tongtongwang86/Revolute/Misc/Pictures V3/configurator/consumer.webp

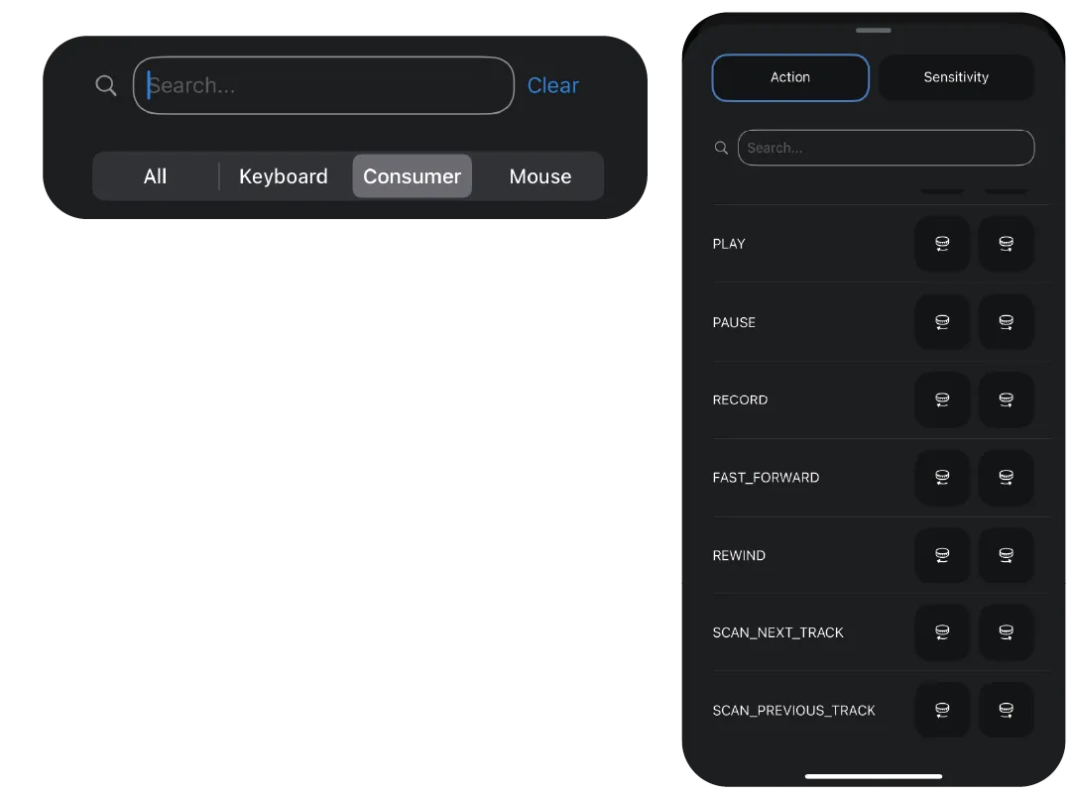
Misc/Pictures V3/configurator/consumer.webp
