tongtongwang86/Revolute/Misc/Pictures V3/configurator/dial.png

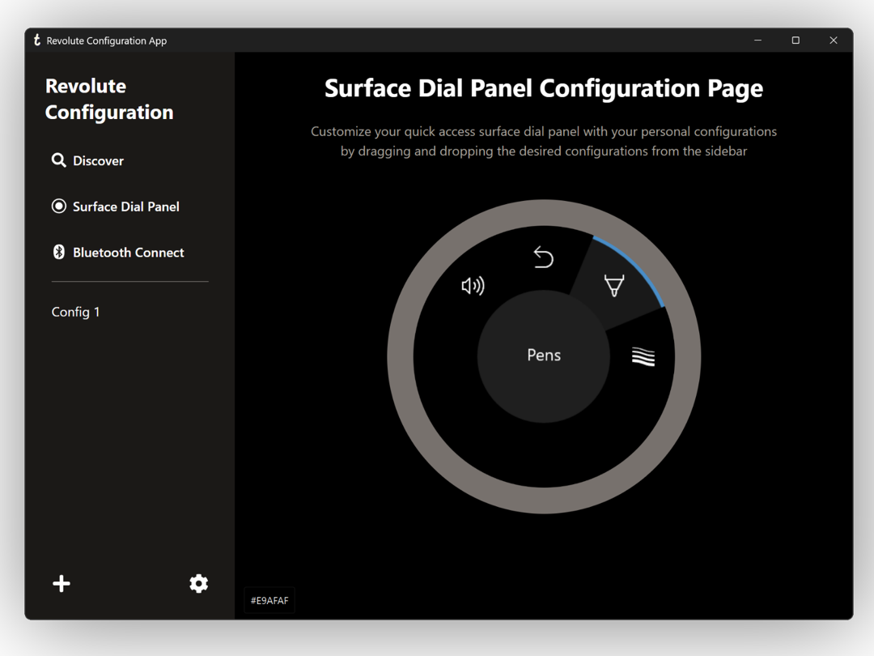
Misc/Pictures V3/configurator/dial.png
