tongtongwang86/Revolute/Misc/Pictures V3/configurator/mouse.webp

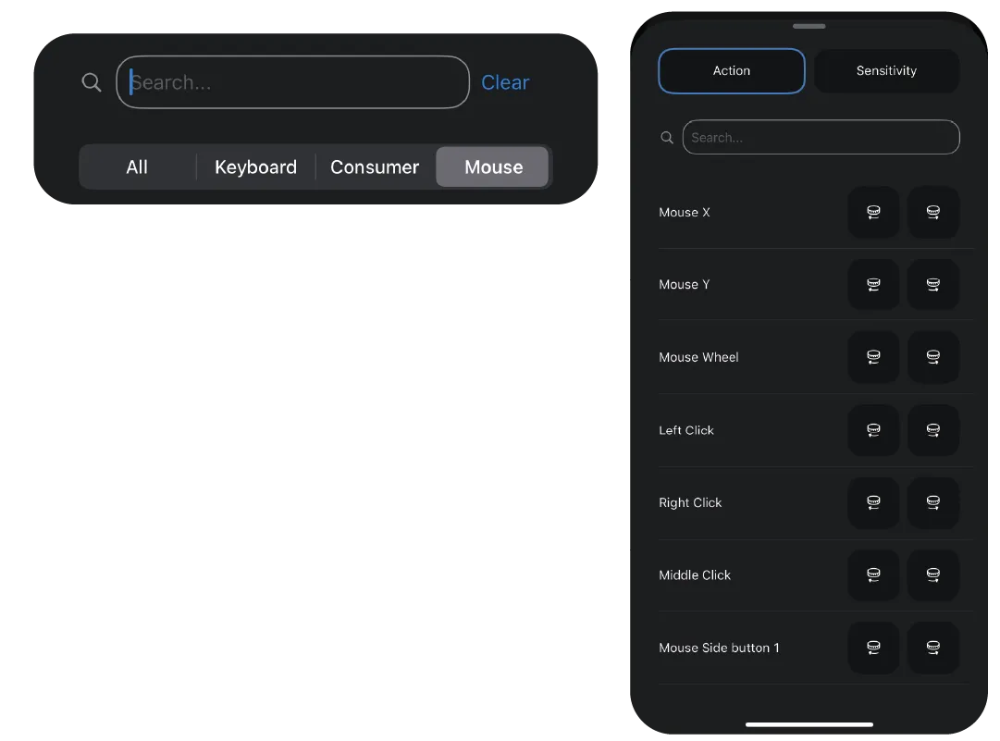
Misc/Pictures V3/configurator/mouse.webp
