tongtongwang86/Revolute/Misc/Pictures V3/configurator/scroll.webp

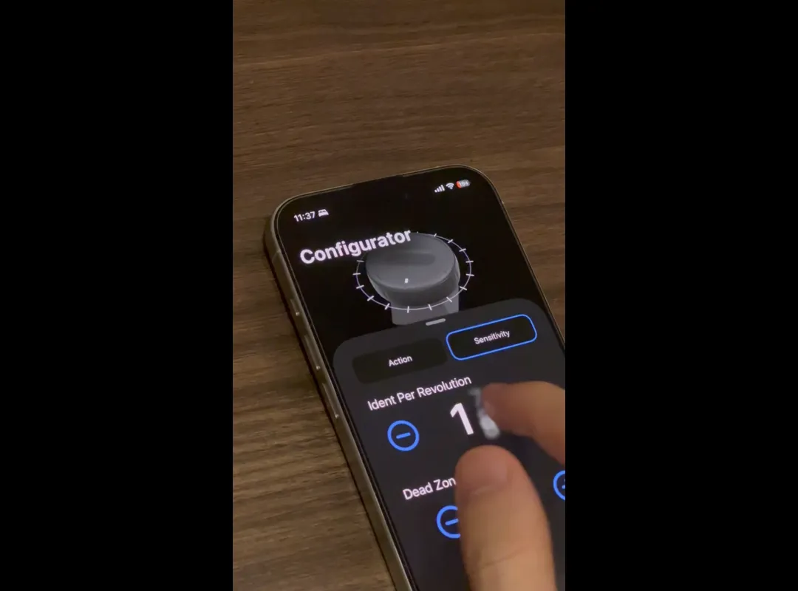
Misc/Pictures V3/configurator/scroll.webp
