tongtongwang86/Revolute/Misc/Pictures V3/demo/1.png

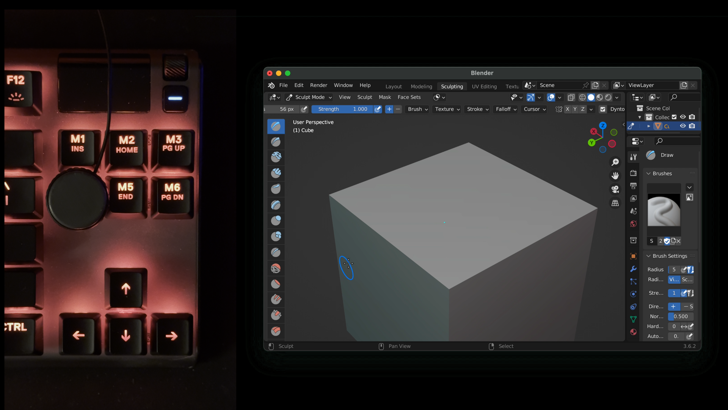
Misc/Pictures V3/demo/1.png
