tongtongwang86/Revolute/Misc/Pictures V3/demo/2.png

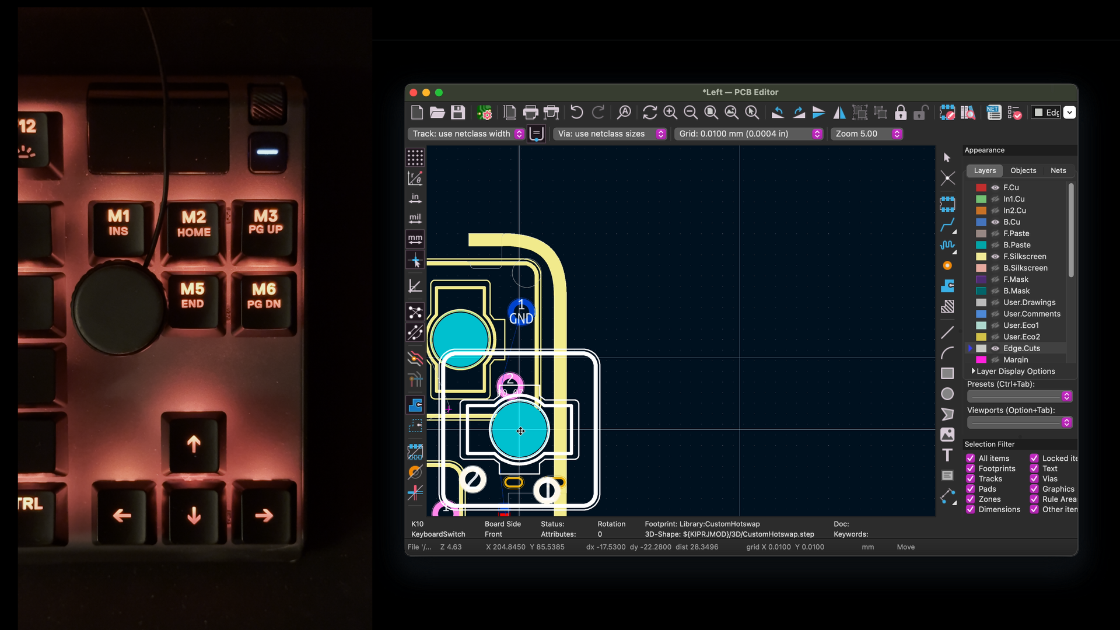
Misc/Pictures V3/demo/2.png
