tongtongwang86/Revolute/Misc/Pictures V3/demo/3.png

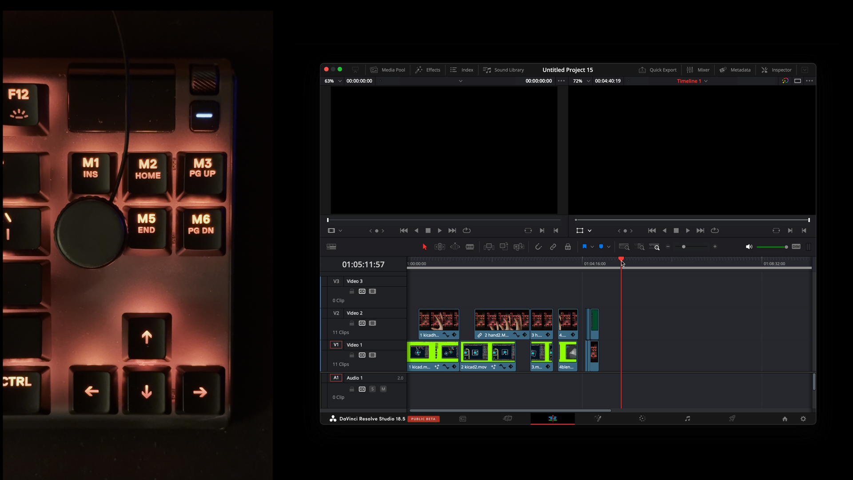
Misc/Pictures V3/demo/3.png
