tongtongwang86/Revolute/Misc/Pictures V3/demo/3_Small.png

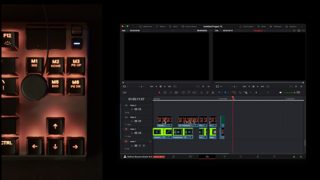
Misc/Pictures V3/demo/3_Small.png
