tongtongwang86/Revolute/Misc/Pictures V3/demo/4.png

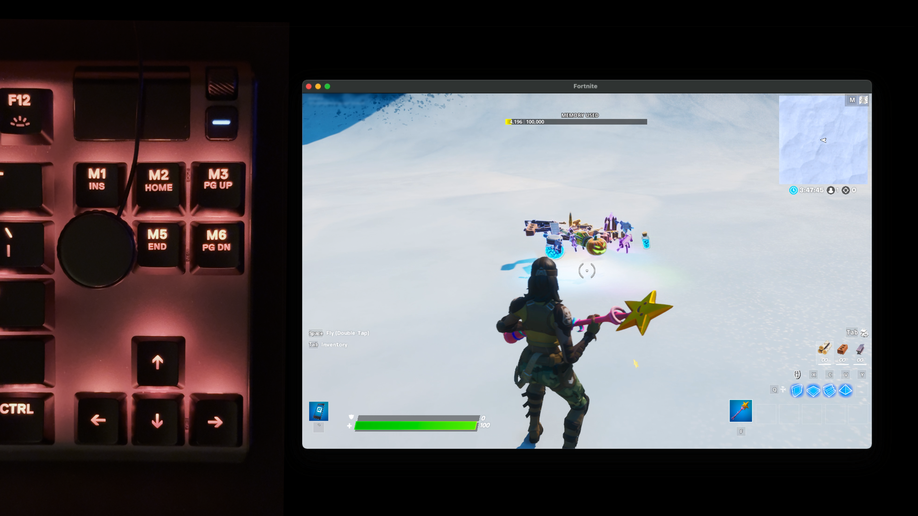
Misc/Pictures V3/demo/4.png
