tongtongwang86/Revolute/Misc/Pictures V3/poster/magtick.png

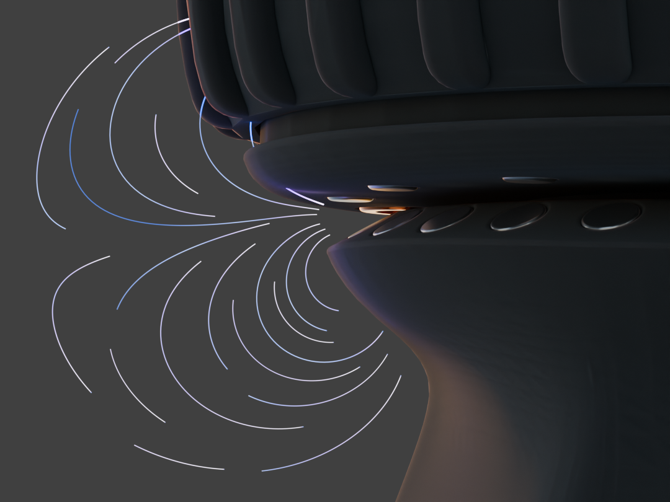
Misc/Pictures V3/poster/magtick.png
