tongtongwang86/Revolute/Hardware/Wired/TopPCB/TopPCB.step

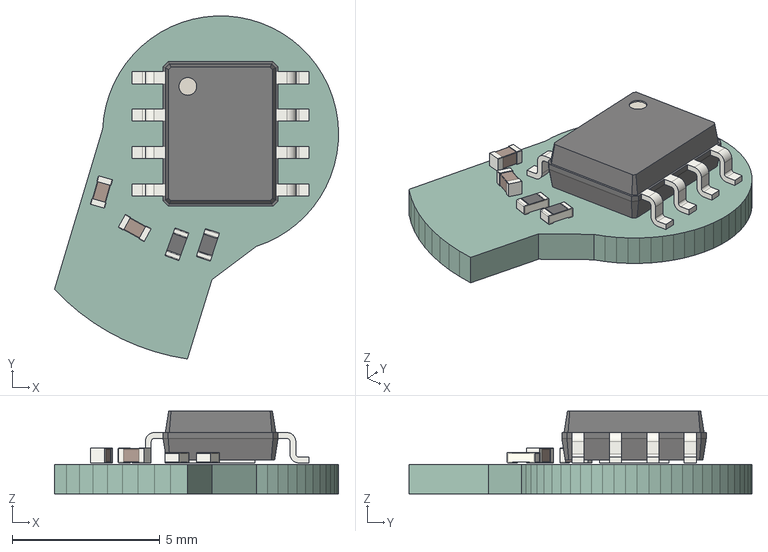
[picture p36: CAD file, 2023-05-05]
Hardware/Wired/TopPCB/TopPCB.step
9.63 x 11.6 x 2.80 mm
PCB
