tongtongwang86/Revolute/Hardware/Wired/TopPCB/wire.stl

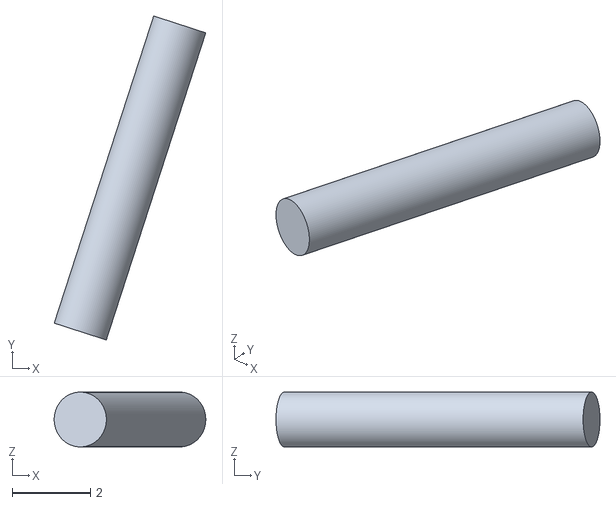
[picture p37: CAD file, 2023-05-05]
Hardware/Wired/TopPCB/wire.stl
3.87 x 8.27 x 1.40
