tongtongwang86/Revolute/Hardware/Debugger/3D/button v4.step

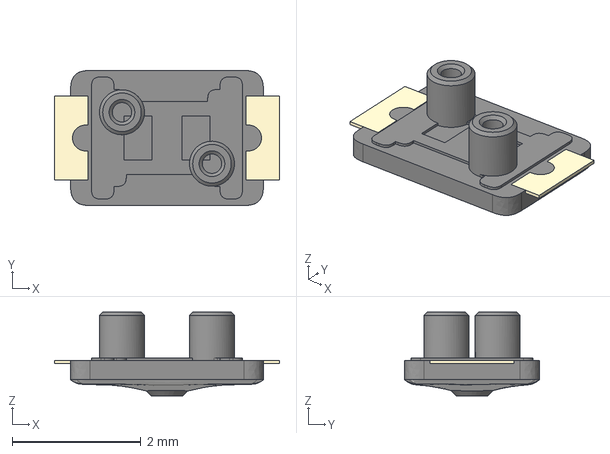
[picture p38: CAD file, 2024-02-21]
Hardware/Debugger/3D/button v4.step
3.50 x 2.10 x 1.30 mm
base
slider
