tongtongwang86/Revolute/Hardware/Debugger/3D/pogo_T1836 v1.step

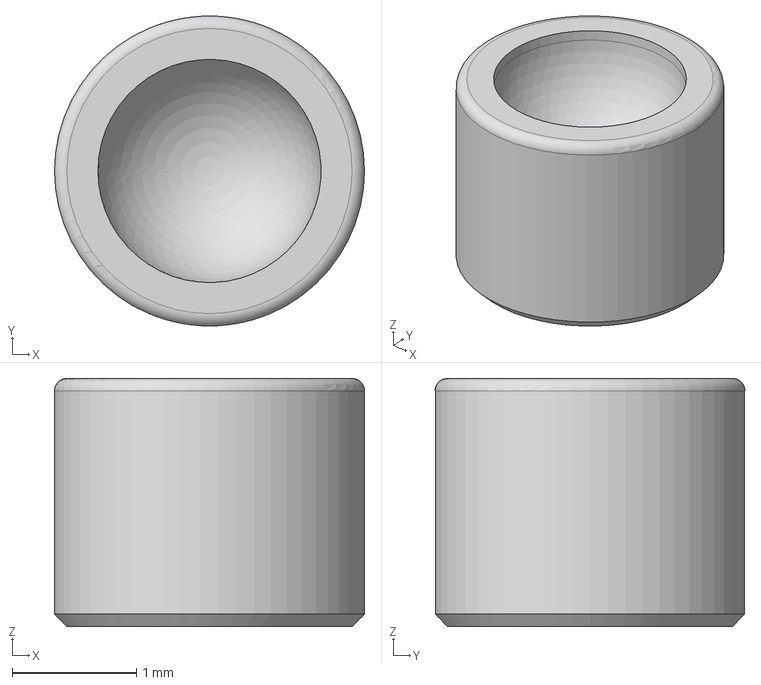
[picture p39: CAD file, 2024-01-14]
Hardware/Debugger/3D/pogo_T1836 v1.step
2.50 x 2.50 x 2.00 mm
