tongtongwang86/Revolute/Hardware/Debuggerbmp/3D/buttoncompliant v4.step

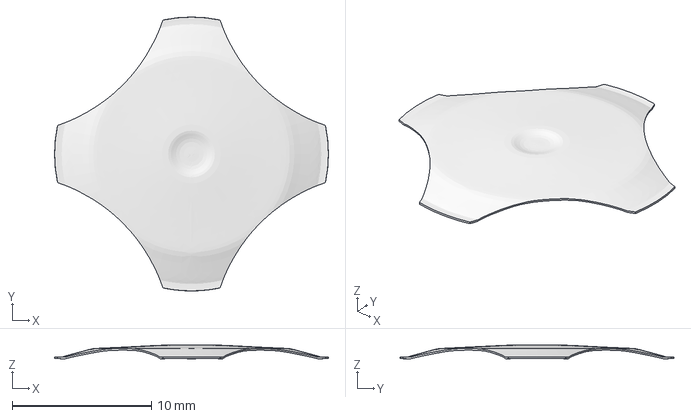
[picture p40: CAD file, 2024-01-14]
Hardware/Debuggerbmp/3D/buttoncompliant v4.step
19.7 x 19.7 x 0.979 mm
