tongtongwang86/Revolute/Hardware/Debugger/3D/m3808 pogofemale v3.step

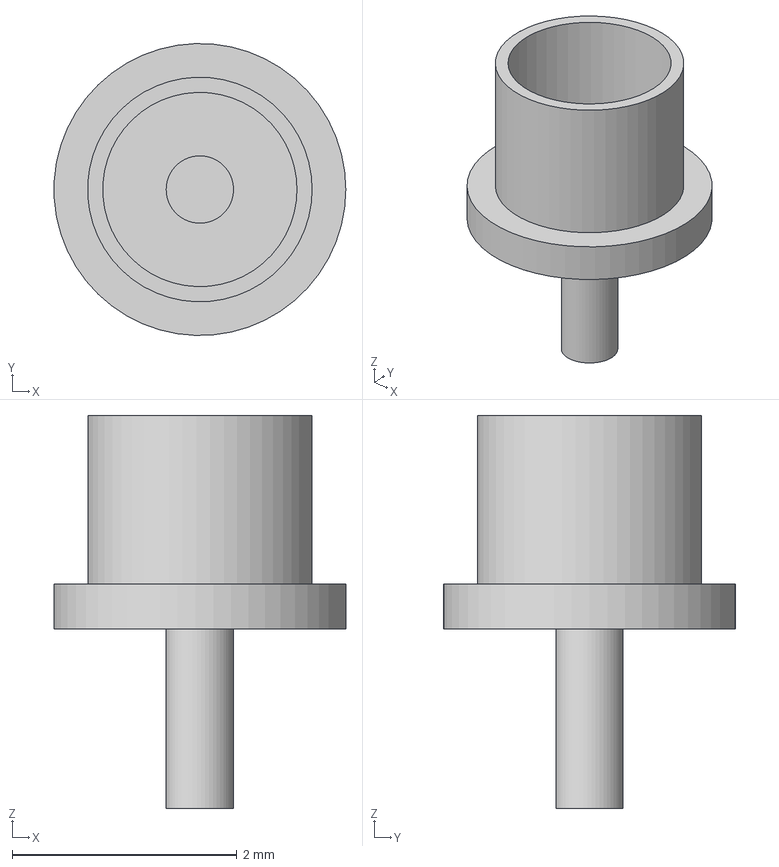
[picture p41: CAD file, 2024-01-13]
Hardware/Debugger/3D/m3808 pogofemale v3.step
2.60 x 2.60 x 3.50 mm
