tongtongwang86/Revolute/Hardware/Debugger/3D/KailhChocV2.step

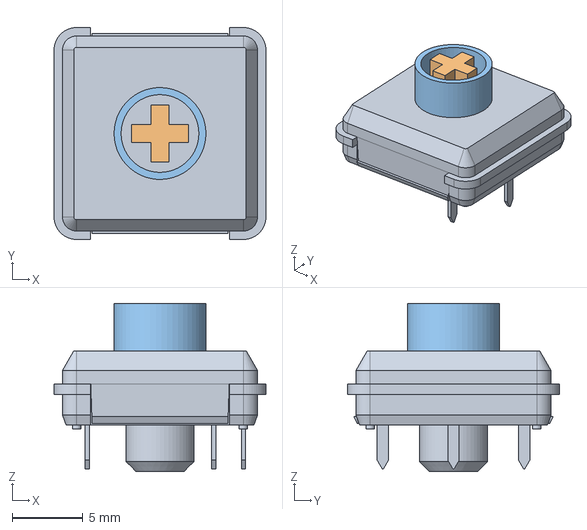
[picture p42: CAD file, 2023-12-28]
Hardware/Debugger/3D/KailhChocV2.step
15.0 x 15.0 x 11.9 mm
Plunger
