tongtongwang86/Revolute/Hardware/Debuggerbmp/3D/USB - C inboard.step

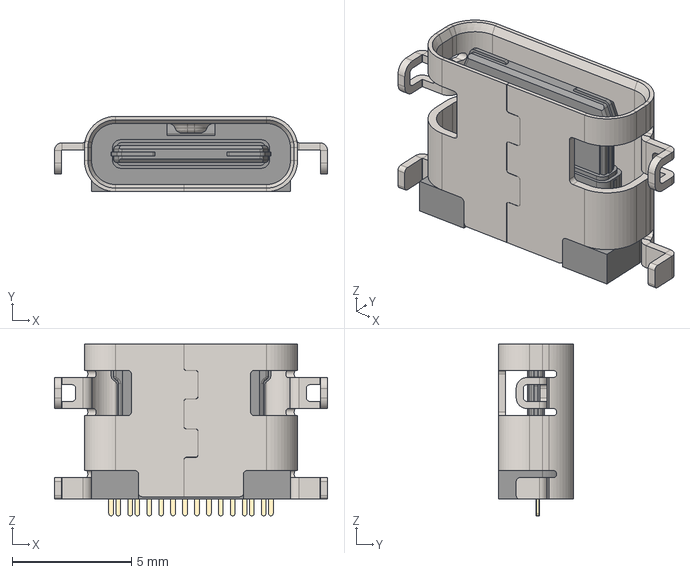
[picture p43: CAD file, 2023-12-28]
Hardware/Debuggerbmp/3D/USB - C inboard.step
11.5 x 3.16 x 7.20 mm
USB-C inboard metal
USB-C plastic
