tongtongwang86/Revolute/Hardware/Wired/MainPCB/3d/BK13C06-10DP2-0.35V_3D_STP.stp

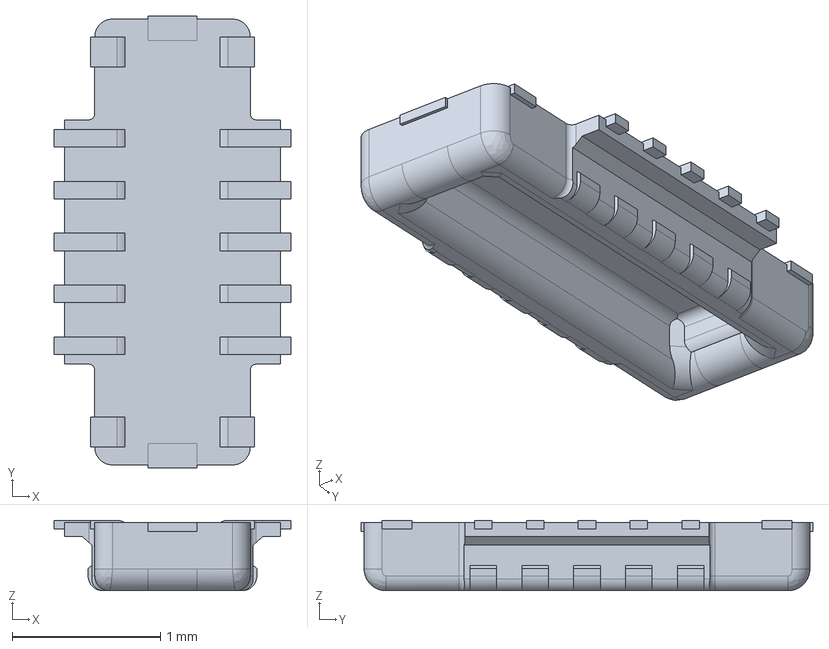
[picture p44: CAD file, 2023-12-27]
Hardware/Wired/MainPCB/3d/BK13C06-10DP2-0.35V_3D_STP.stp
1.60 x 3.05 x 0.475 mm
