tongtongwang86/Revolute/Hardware/Debuggerbmp/3D/GateronHotswap v3.step

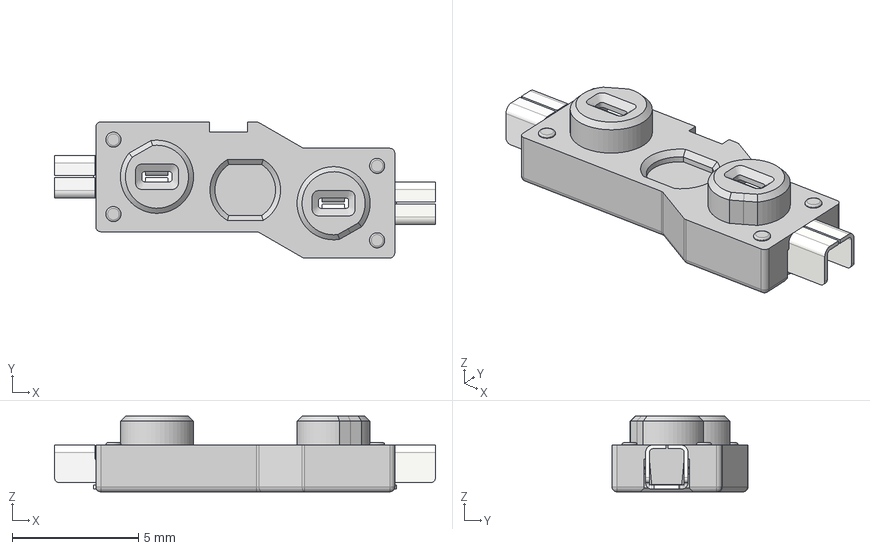
[picture p45: CAD file, 2023-12-28]
Hardware/Debuggerbmp/3D/GateronHotswap v3.step
15.1 x 5.39 x 3.00 mm
