tongtongwang86/Revolute/Hardware/Wired/MainPCB/3d/BK13C06-10DS2-0.35V_3D_STP.stp

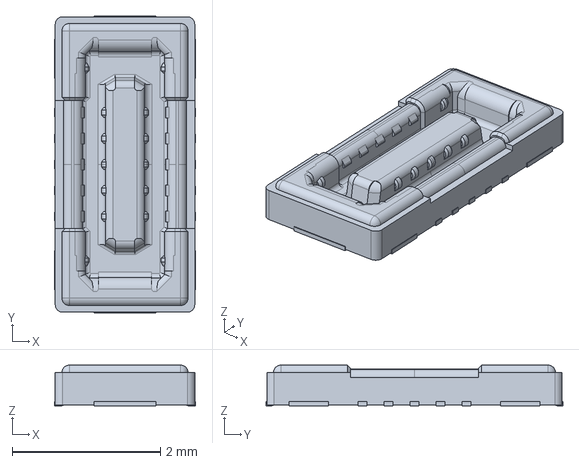
[picture p46: CAD file, 2023-12-27]
Hardware/Wired/MainPCB/3d/BK13C06-10DS2-0.35V_3D_STP.stp
1.90 x 4.00 x 0.55 mm
