tongtongwang86/Revolute/Hardware/Debugger/3D/256Mbit GD25Q.step

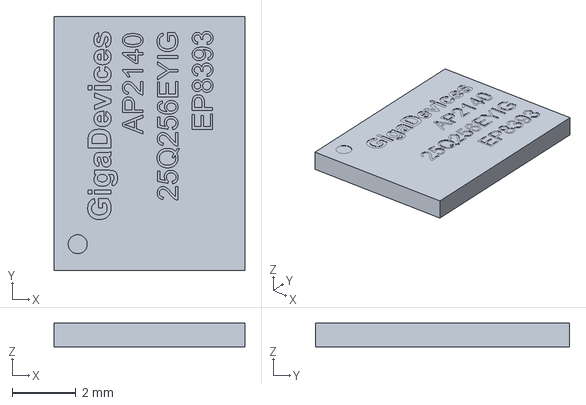
[picture p47: CAD file, 2023-12-28]
Hardware/Debugger/3D/256Mbit GD25Q.step
6.00 x 8.00 x 0.75 mm
