tongtongwang86/Revolute/Hardware/Wired/MainPCB/3d/button3.step

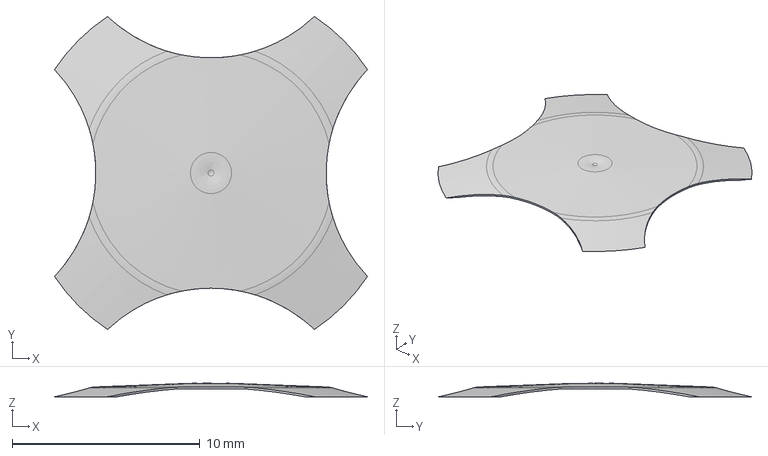
[picture p48: CAD file, 2023-12-27]
Hardware/Wired/MainPCB/3d/button3.step
16.7 x 16.7 x 0.722 mm
