tongtongwang86/Revolute/Hardware/Debugger/3D/Humidity.step

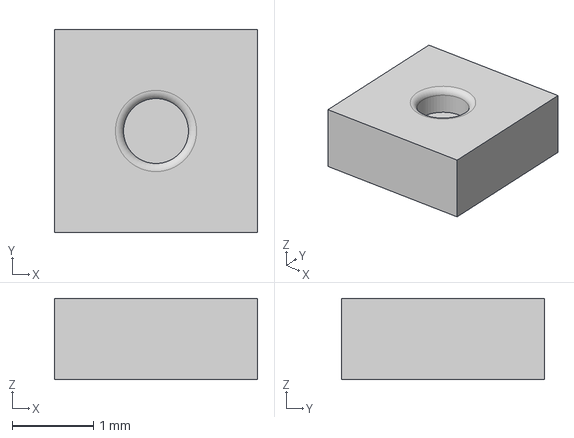
[picture p49: CAD file, 2023-12-28]
Hardware/Debugger/3D/Humidity.step
2.50 x 2.50 x 1.00 mm
