tongtongwang86/Revolute/Hardware/Debuggerbmp/3D/Inductor v1.step

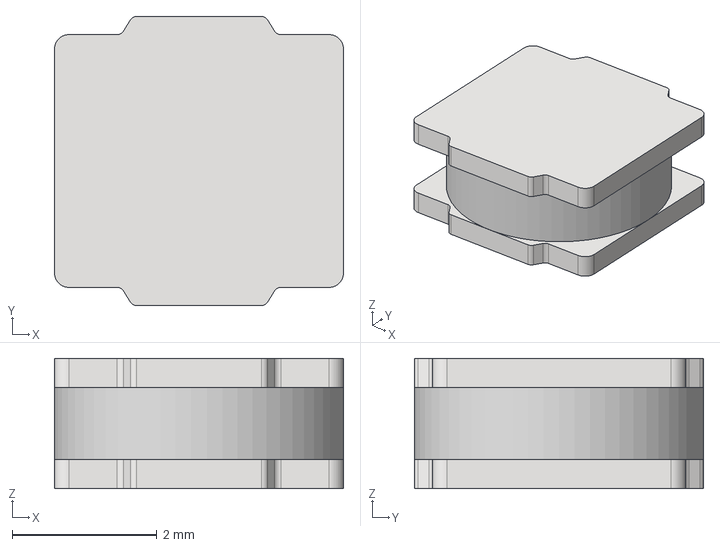
[picture p50: CAD file, 2023-12-28]
Hardware/Debuggerbmp/3D/Inductor v1.step
4.00 x 4.00 x 1.80 mm
