tongtongwang86/Revolute/Hardware/Debugger/3D/APDS-9960.step

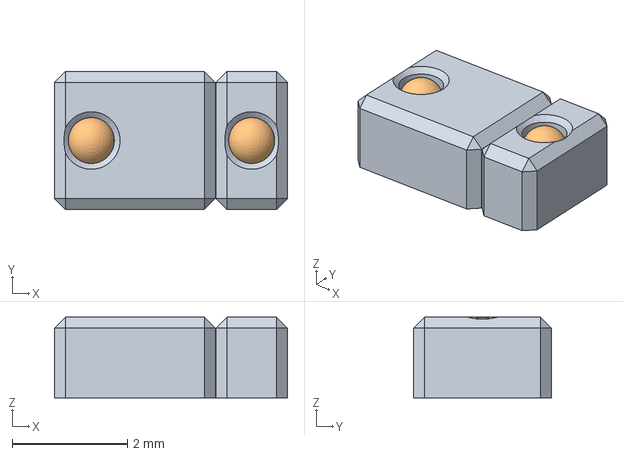
[picture p51: CAD file, 2023-12-28]
Hardware/Debugger/3D/APDS-9960.step
4.05 x 2.40 x 1.40 mm
