tongtongwang86/Revolute/Hardware/Wired/MainPCB/3d/WLCSP94_3P5X3P6_NOR.step

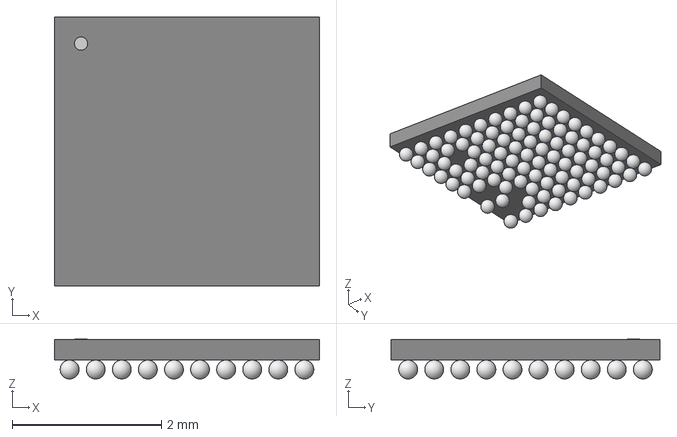
[picture p52: CAD file, 2023-12-27]
Hardware/Wired/MainPCB/3d/WLCSP94_3P5X3P6_NOR.step
3.56 x 3.61 x 0.536 mm
