tongtongwang86/Revolute/Hardware/Debugger/3D/LedV2 v4.step

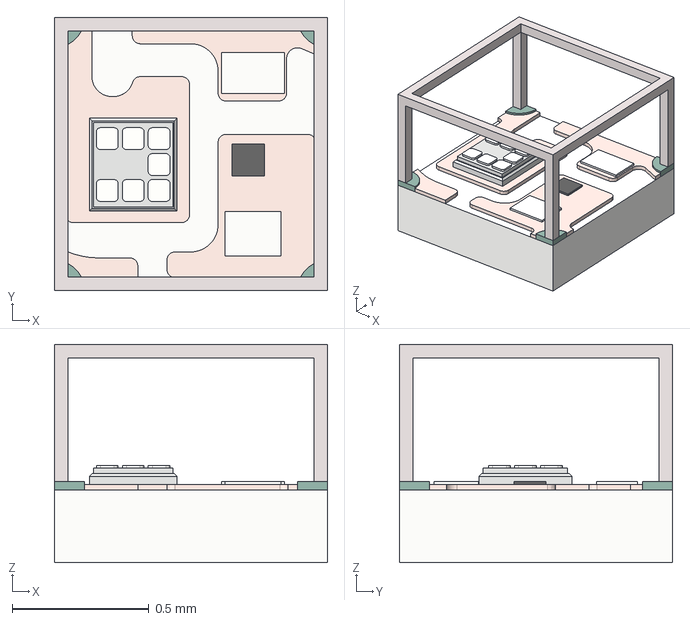
[picture p53: CAD file, 2023-12-28]
Hardware/Debugger/3D/LedV2 v4.step
1.00 x 1.00 x 0.8 mm
