tongtongwang86/Revolute/Hardware/Debuggerbmp/3D/Antenna.step

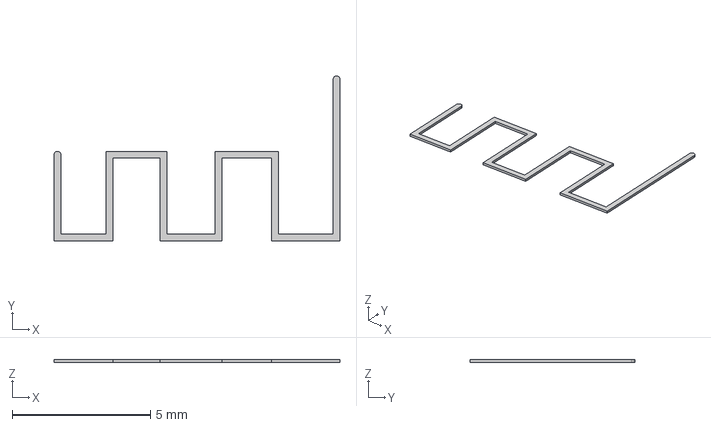
[picture p54: CAD file, 2023-12-28]
Hardware/Debuggerbmp/3D/Antenna.step
10.3 x 5.98 x 0.1 mm
