tongtongwang86/Revolute/Hardware/Wired/MainPCB/3d/32MHZ Clock v1.step

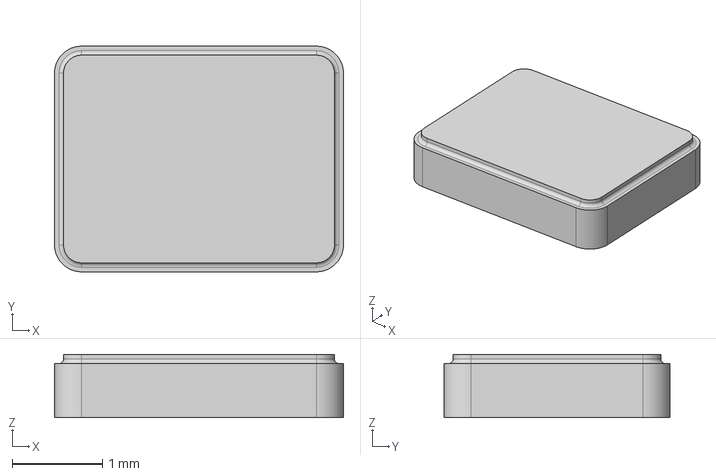
[picture p55: CAD file, 2023-06-28]
Hardware/Wired/MainPCB/3d/32MHZ Clock v1.step
3.20 x 2.50 x 0.7 mm
