tongtongwang86/Revolute/Hardware/Wired/MainPCB/3d/Crystal 2 v0.step

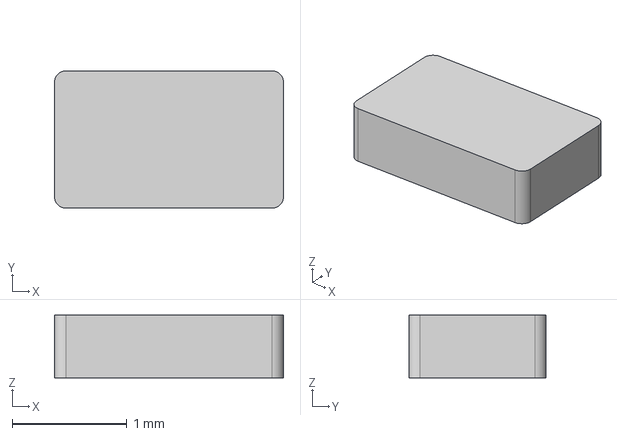
[picture p56: CAD file, 2023-06-28]
Hardware/Wired/MainPCB/3d/Crystal 2 v0.step
2.00 x 1.20 x 0.55 mm
