tongtongwang86/Revolute/Hardware/Debugger/3D/Pdmmic.step

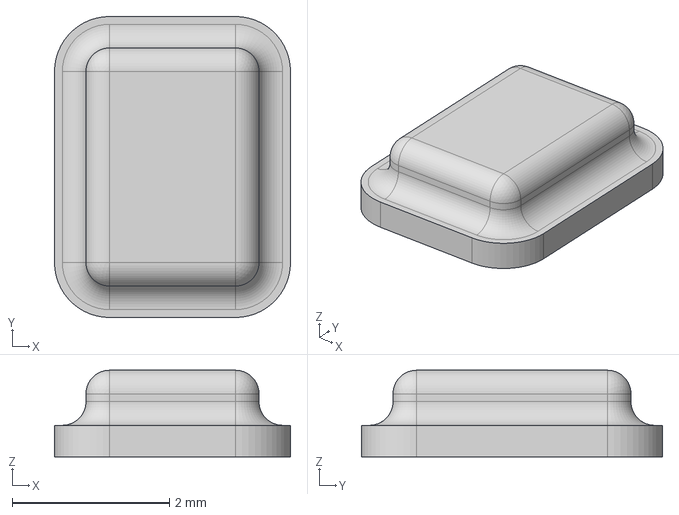
[picture p57: CAD file, 2023-12-28]
Hardware/Debugger/3D/Pdmmic.step
3.00 x 3.83 x 1.10 mm
