tongtongwang86/Revolute/Hardware/Wired/MainPCB/3d/USB2 v3.step

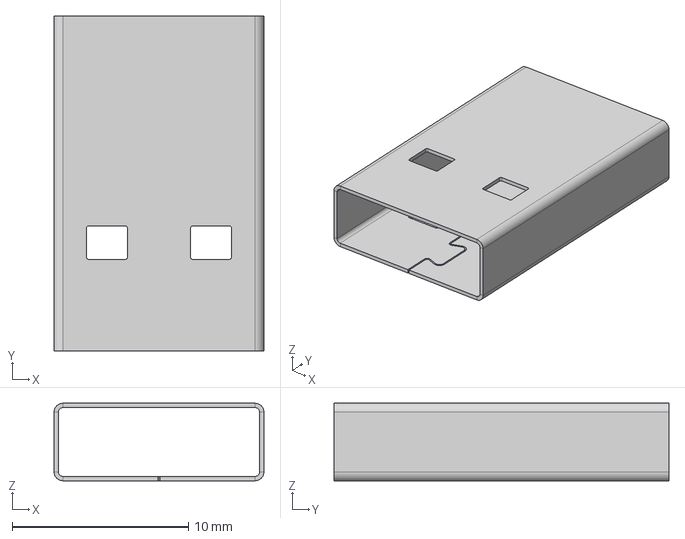
[picture p58: CAD file, 2022-10-10]
Hardware/Wired/MainPCB/3d/USB2 v3.step
11.9 x 19.0 x 4.40 mm
