tongtongwang86/Revolute/Hardware/Wired/MainPCB/3d/SW_Hotswap_Kailh_Choc_v1.stp

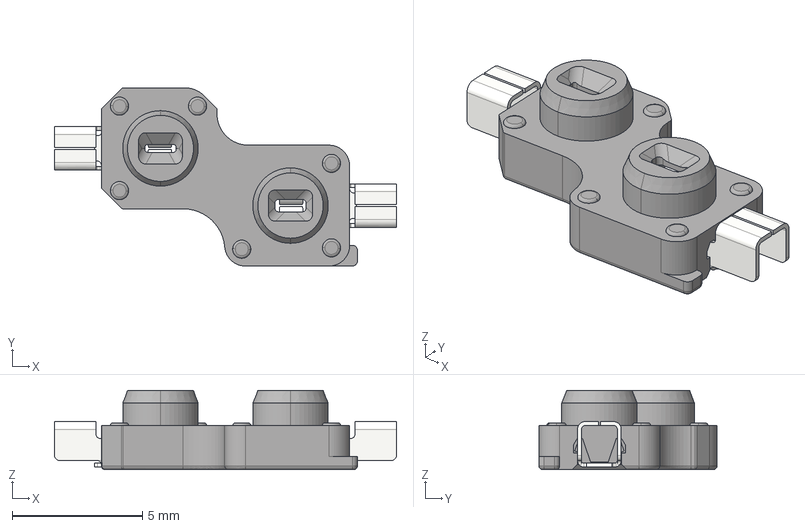
[picture p59: CAD file, 2022-10-10]
Hardware/Wired/MainPCB/3d/SW_Hotswap_Kailh_Choc_v1.stp
13.2 x 6.85 x 3.05 mm
