tongtongwang86/Revolute/Hardware/Wired/MainPCB/3d/Battery2 v1.step

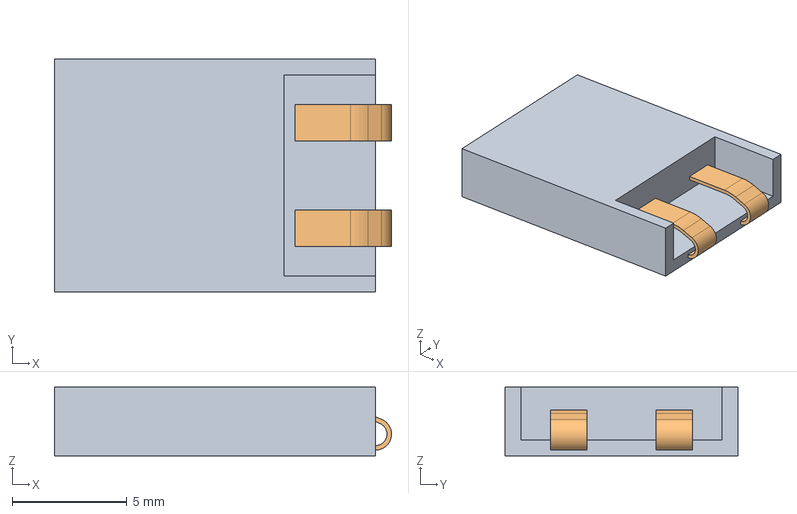
[picture p60: CAD file, 2022-10-10]
Hardware/Wired/MainPCB/3d/Battery2 v1.step
14.7 x 10.2 x 3.00 mm
