tongtongwang86/Revolute/Hardware/Wired/MainPCB/3d/Battery v2.step

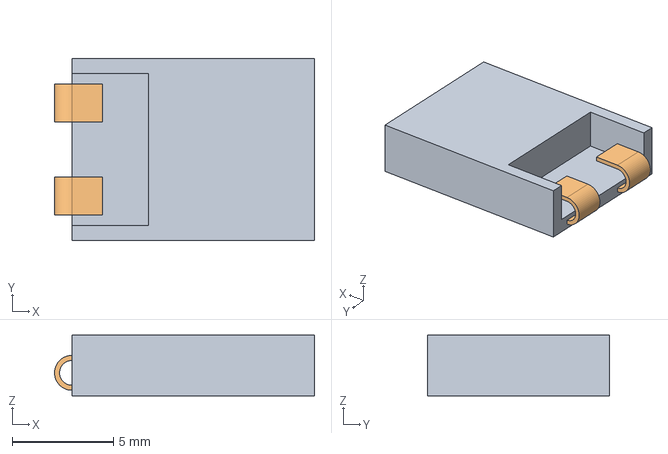
[picture p61: CAD file, 2022-10-10]
Hardware/Wired/MainPCB/3d/Battery v2.step
12.9 x 9.00 x 3.00 mm
